Tubbz-alt/LaserHarp/Arduino/LaserHarp/vs1053midi.h

#define instr_acoustic_grand_piano 0    // Acoustic Grand Piano
#define instr_bright_acoustic_piano 1   // Bright Acoustic Piano
#define instr_electric_grand_piano 2    // Electric Grand Piano
#define instr_honky_tonk_piano 3        // Honky-tonk Piano
#define instr_electric_piano_1 4        // Electric Piano 1
#define instr_electric_piano_2 5        // Electric Piano 2
#define instr_harpsichord 6             // Harpsichord
#define instr_clavi 7                   // Clavi
#define instr_celesta 8                 // Celesta
#define instr_glockenspiel 9            // Glockenspiel
#define instr_music_box 10              // Music Box
#define instr_vibraphone 11             // Vibraphone
#define instr_marimba 12                // Marimba
#define instr_xylophone 13              // Xylophone
#define instr_tubular_bells 14          // Tubular Bells
#define instr_dulcimer 15               // Dulcimer
#define instr_drawbar_organ 16          // Drawbar Organ
#define instr_percussive_organ 17       // Percussive Organ
#define instr_rock_organ 18             // Rock Organ
#define instr_church_organ 19           // Church Organ
#define instr_reed_organ 20             // Reed Organ
#define instr_accordion 21              // Accordion
#define instr_harmonica 22              // Harmonica
#define instr_tango_accordion 23        // Tango Accordion
#define instr_acoustic_guitar__nylon 24 // Acoustic Guitar (nylon)
#define instr_acoustic_guitar__steel 25 // Acoustic Guitar (steel)
#define instr_electric_guitar__jazz 26  // Electric Guitar (jazz)
#define instr_electric_guitar__clean 27 // Electric Guitar (clean)
#define instr_electric_guitar__muted 28 // Electric Guitar (muted)
#define instr_overdriven_guitar 29      // Overdriven Guitar
#define instr_distortion_guitar 30      // Distortion Guitar
#define instr_guitar_harmonics 31       // Guitar Harmonics
#define instr_acoustic_bass 32          // Acoustic Bass
#define instr_electric_bass__finger 33  // Electric Bass (finger)
#define instr_electric_bass__pick 34    // Electric Bass (pick)
#define instr_fretless_bass 35          // Fretless Bass
#define instr_slap_bass_1 36            // Slap Bass 1
#define instr_slap_bass_2 37            // Slap Bass 2
#define instr_synth_bass_1 38           // Synth Bass 1
#define instr_synth_bass_2 39           // Synth Bass 2
#define instr_violin 40                 // Violin
#define instr_viola 41                  // Viola
#define instr_cello 42                  // Cello
#define instr_contrabass 43             // Contrabass
#define instr_tremolo_strings 44        // Tremolo Strings
#define instr_pizzicato_strings 45      // Pizzicato Strings
#define instr_orchestral_harp 46        // Orchestral Harp
#define instr_timpani 47                // Timpani
#define instr_string_ensembles_1 48     // String Ensembles 1
#define instr_string_ensembles_2 49     // String Ensembles 2
#define instr_synth_strings_1 50        // Synth Strings 1
#define instr_synth_strings_2 51        // Synth Strings 2
#define instr_choir_aahs 52             // Choir Aahs
#define instr_voice_oohs 53             // Voice Oohs
#define instr_synth_voice 54            // Synth Voice
#define instr_orchestra_hit 55          // Orchestra Hit
#define instr_trumpet 56                // Trumpet
#define instr_trombone 57               // Trombone
#define instr_tuba 58                   // Tuba
#define instr_muted_trumpet 59          // Muted Trumpet
#define instr_french_horn 60            // French Horn
#define instr_brass_section 61          // Brass Section
#define instr_synth_brass_1 62          // Synth Brass 1
#define instr_synth_brass_2 63          // Synth Brass 2
#define instr_soprano_sax 64            // Soprano Sax
#define instr_alto_sax 65               // Alto Sax
#define instr_tenor_sax 66              // Tenor Sax
#define instr_baritone_sax 67           // Baritone Sax
#define instr_oboe 68                   // Oboe
#define instr_english_horn 69           // English Horn
#define instr_bassoon 70                // Bassoon
#define instr_clarinet 71               // Clarinet
#define instr_piccolo 72                // Piccolo
#define instr_flute 73                  // Flute
#define instr_recorder 74               // Recorder
#define instr_pan_flute 75              // Pan Flute
#define instr_blown_bottle 76           // Blown Bottle
#define instr_shakuhachi 77             // Shakuhachi
#define instr_whistle 78                // Whistle
#define instr_ocarina 79                // Ocarina
#define instr_square_lead__lead1 80     // Square Lead (Lead1)
#define instr_sainstr_w_lead__lead 81         // Saw Lead (Lead)
#define instr_calliope_lead__lead3 82   // Calliope Lead (Lead3)
#define instr_chiff_lead__lead4 83      // Chiff Lead (Lead4)
#define instr_charang_lead__lead5 84    // Charang Lead (Lead5)
#define instr_voice_lead__lead6 85      // Voice Lead (Lead6)
#define instr_fifths_lead__lead7 86     // Fifths Lead (Lead7)
#define instr_bass_and_lead__lead8 87   // Bass + Lead (Lead8)
#define instr_new_age__pad1 88          // New Age (Pad1)
#define instr_warm_pad__pad2 89         // Warm Pad (Pad2)
#define instr_polysynth__pad3 90        // Polysynth (Pad3)
#define instr_choir__pad4 91            // Choir (Pad4)
#define instr_bowed__pad5 92            // Bowed (Pad5)
#define instr_metallic__pad6 93         // Metallic (Pad6)
#define instr_halo__pad7 94             // Halo (Pad7)
#define instr_sweep__pad8 95            // Sweep (Pad8)
#define instr_rain__fx1 96              // Rain (FX1)
#define instr_sound_track__fx2 97       // Sound Track (FX2)
#define instr_crystal__fx3 98           // Crystal (FX3)
#define instr_atmosphere__fx4 99        // Atmosphere (FX4)
#define instr_brightness__fx5 100       // Brightness (FX5)
#define instr_goblins__fx6 101          // Goblins (FX6)
#define instr_echoes__fx7 102           // Echoes (FX7)
#define instr_sci_fi__fx8 103           // Sci-fi (FX8)
#define instr_sitar 104                 // Sitar
#define instr_banjo 105                 // Banjo
#define instr_shamisen 106              // Shamisen
#define instr_koto 107                  // Koto
#define instr_kalimba 108               // Kalimba
#define instr_bag_pipe 109              // Bag Pipe
#define instr_fiddle 110                // Fiddle
#define instr_shanai 111                // Shanai
#define instr_tinkle_bell 112           // Tinkle Bell
#define instr_agogo 113                 // Agogo
#define instr_pitched_percussion 114    // Pitched Percussion
#define instr_woodblock 115             // Woodblock
#define instr_taiko_drum 116            // Taiko Drum
#define instr_melodic_tom 117           // Melodic Tom
#define instr_synth_drum 118            // Synth Drum
#define instr_reverse_cymbal 119        // Reverse Cymbal
#define instr_guitar_fret_noise 120     // Guitar Fret Noise
#define instr_breath_noise 121          // Breath Noise
#define instr_seashore 122              // Seashore
#define instr_bird_tweet 123            // Bird Tweet
#define instr_telephone_ring 124        // Telephone Ring
#define instr_helicopter 125            // Helicopter
#define instr_applause 126              // Applause
#define instr_gunshot 127               // Gunshot
